xiabo-lab/lyrics/screenshot/carlyric-20260717-191904.png

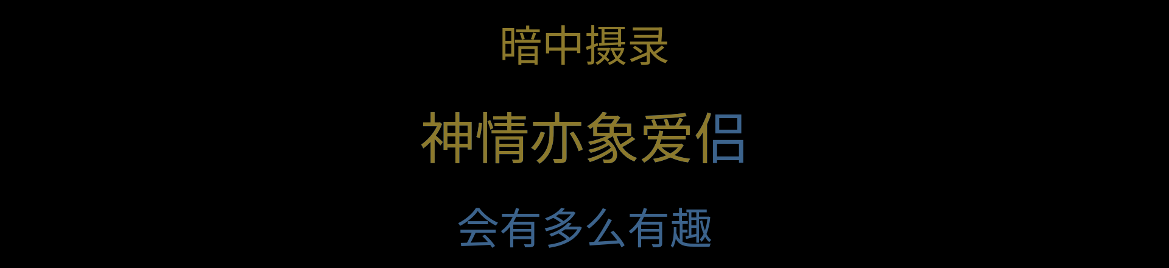
screenshot/carlyric-20260717-191904.png
