xiabo-lab/lyrics/screenshot/carlyric-20260717-194033.png

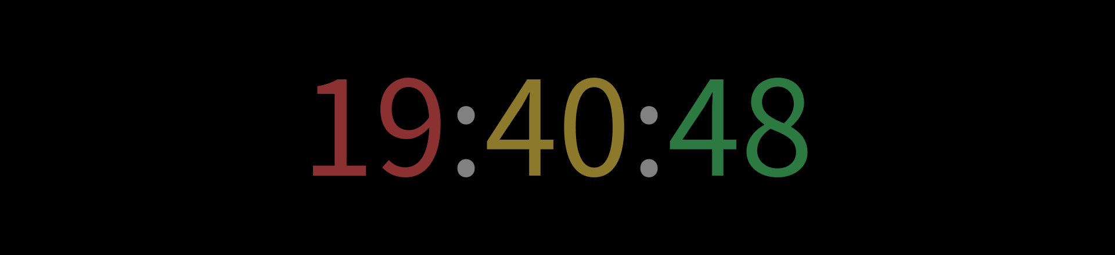
screenshot/carlyric-20260717-194033.png
