xiabo-lab/lyrics/screenshot/carlyric-20260717-194539.png

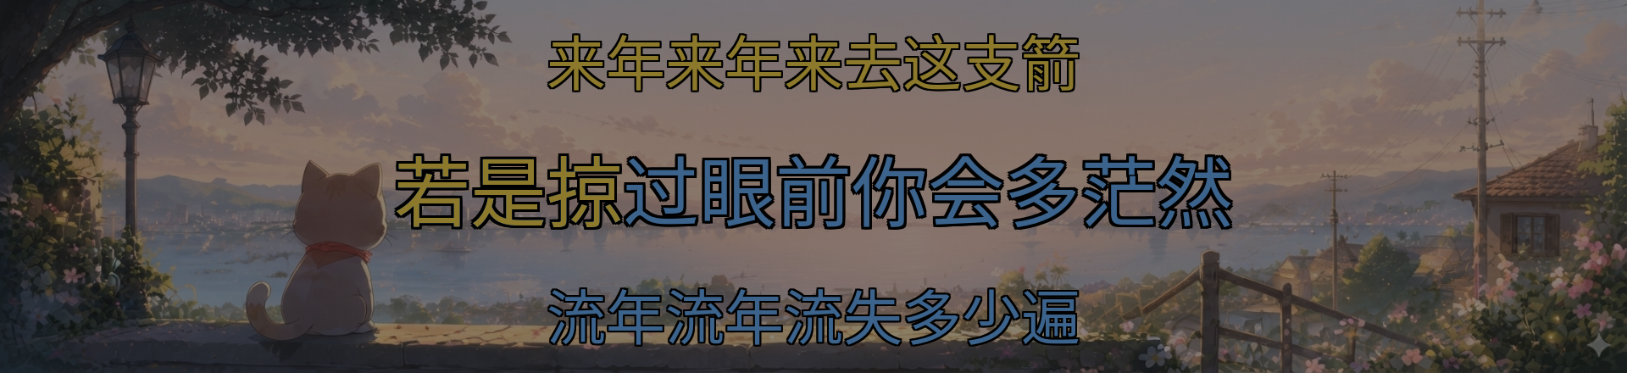
screenshot/carlyric-20260717-194539.png
