xiabo-lab/lyrics/screenshot/carlyric-20260717-200437.png

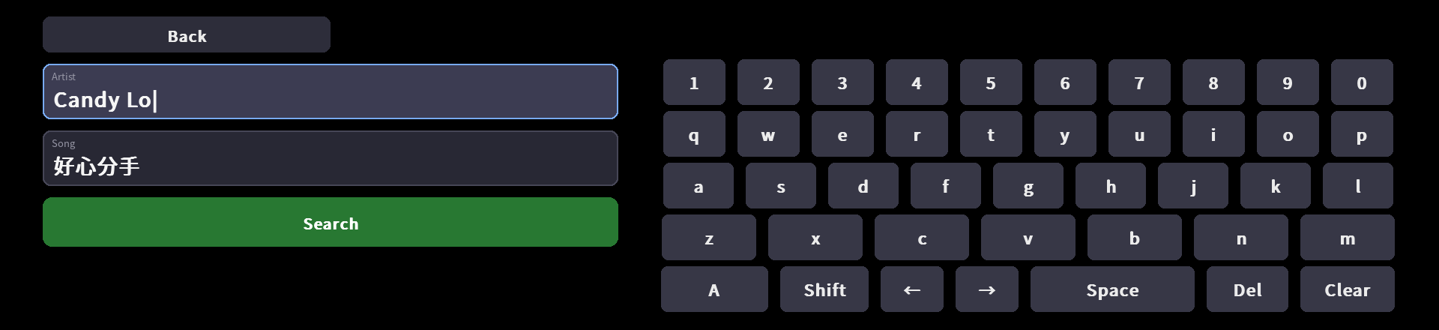
screenshot/carlyric-20260717-200437.png
