xiabo-lab/lyrics/screenshot/live-20260717-205317.png

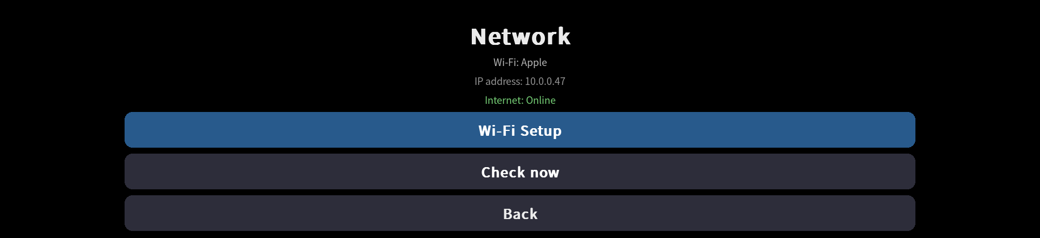
screenshot/live-20260717-205317.png
