xiabo-lab/lyrics/screenshot/menu/01-main-menu.png

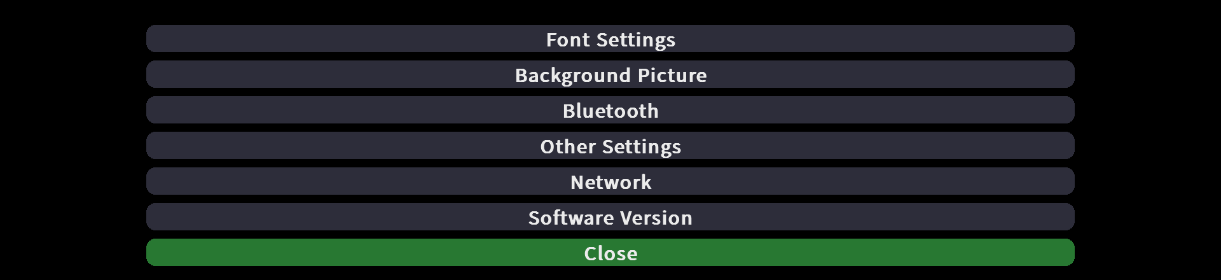
screenshot/menu/01-main-menu.png
