xiabo-lab/lyrics/screenshot/menu/02-font-settings.png

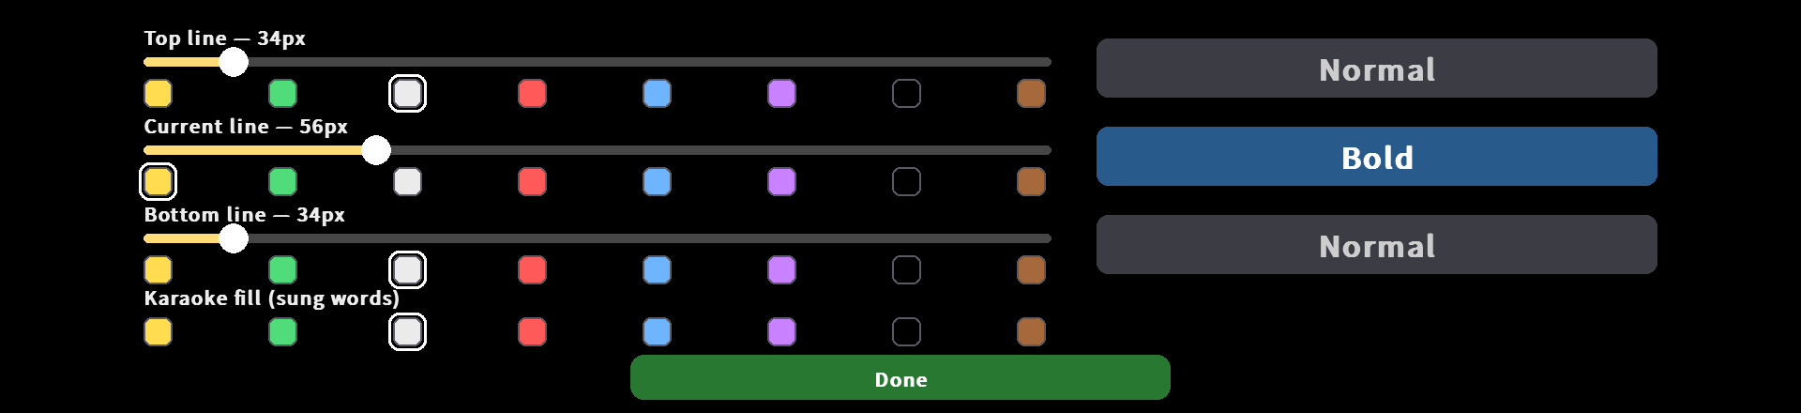
screenshot/menu/02-font-settings.png
