xiabo-lab/lyrics/screenshot/menu/03-background-picture.png

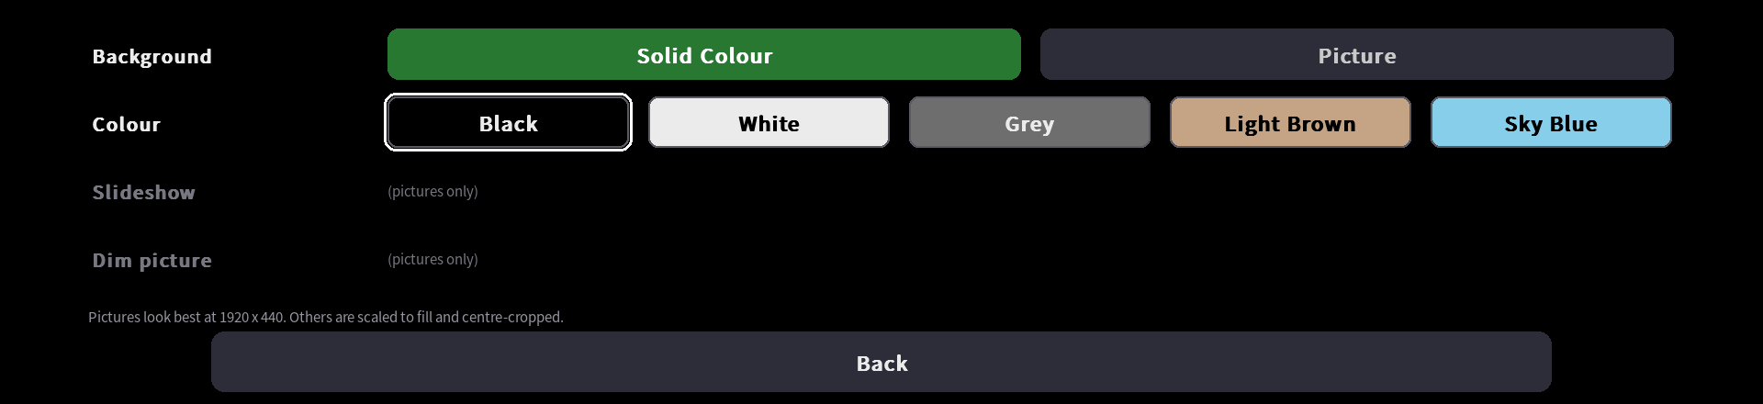
screenshot/menu/03-background-picture.png
