xiabo-lab/lyrics/screenshot/menu/04-bluetooth.png

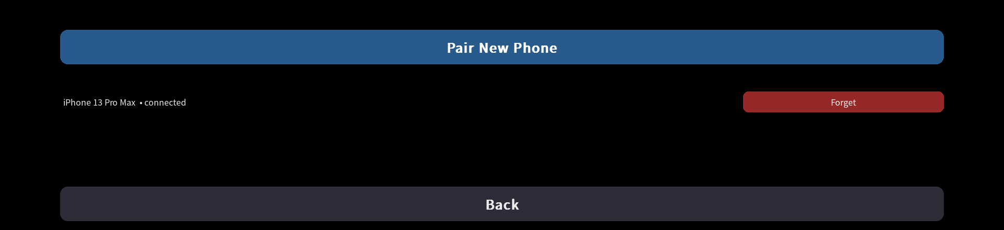
screenshot/menu/04-bluetooth.png
