xiabo-lab/lyrics/screenshot/menu/05-other-settings.png

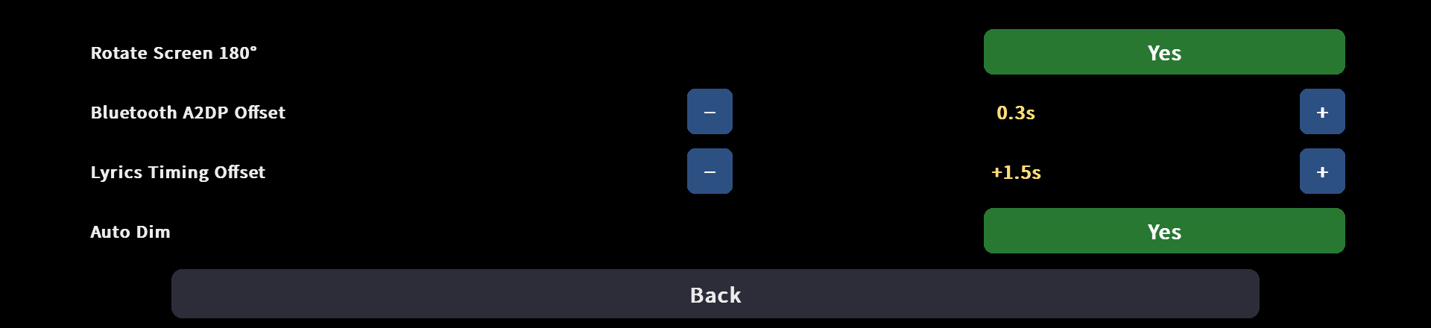
screenshot/menu/05-other-settings.png
