xiabo-lab/lyrics/screenshot/menu/06-network.png

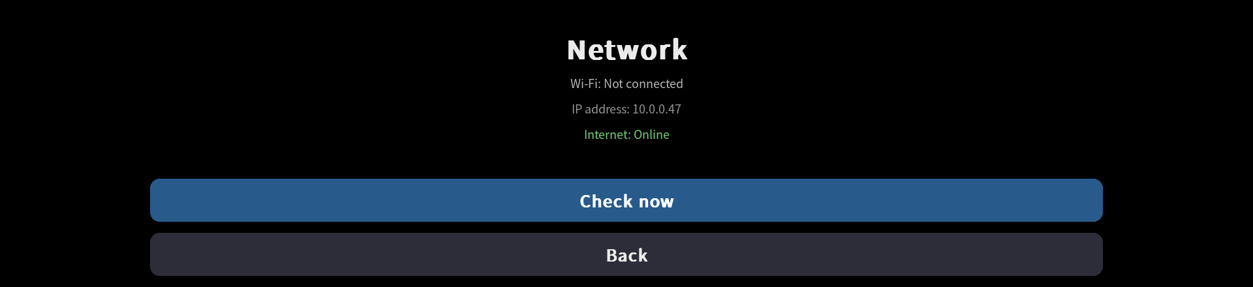
screenshot/menu/06-network.png
