xiabo-lab/lyrics/screenshot/post-ota-20260717-201657.png

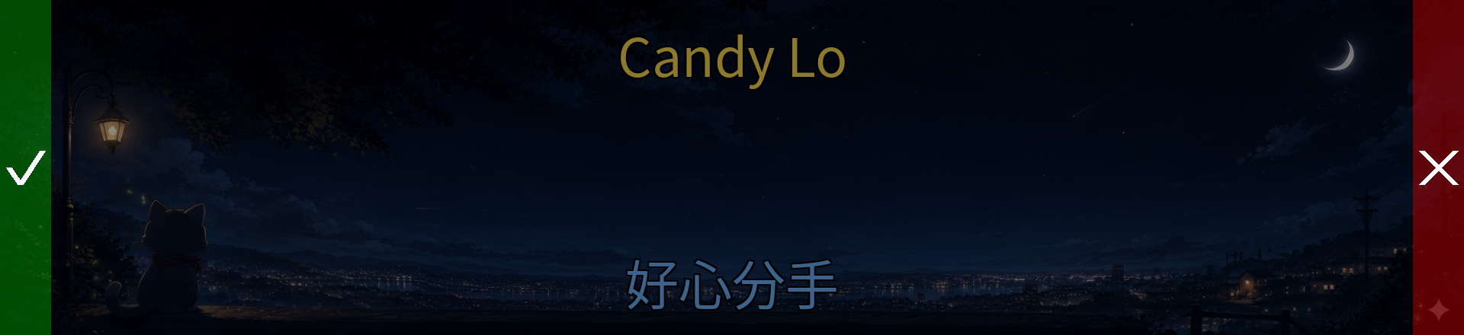
screenshot/post-ota-20260717-201657.png
