xiabo-lab/lyrics/screenshot/wifi/1-list.png

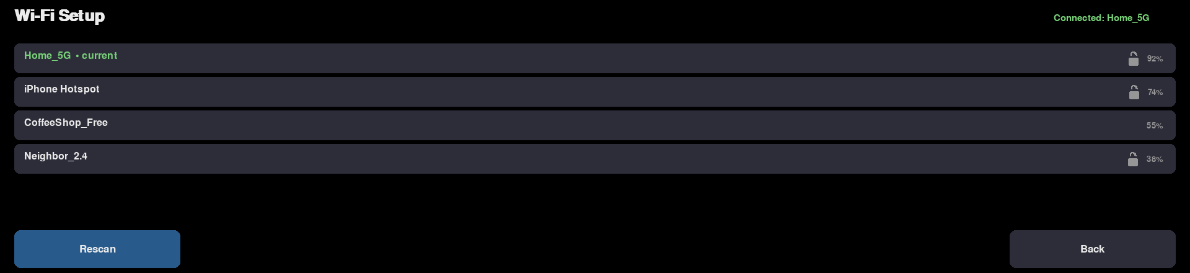
screenshot/wifi/1-list.png
