xiabo-lab/lyrics/screenshot/wifi/2-password.png

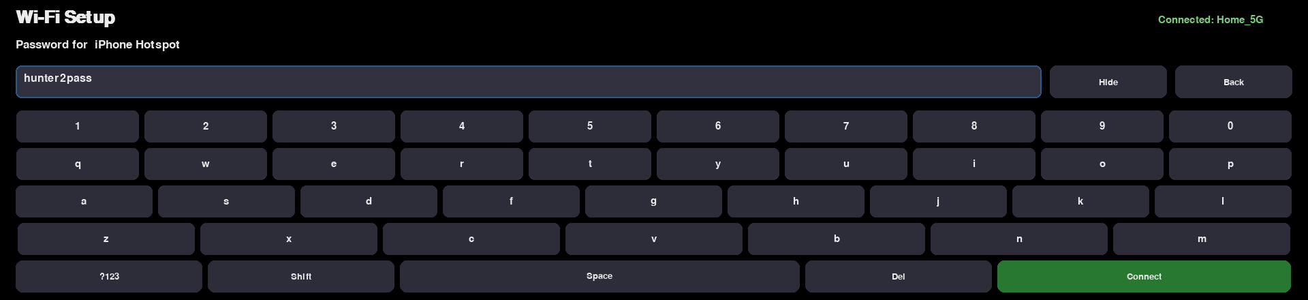
screenshot/wifi/2-password.png
