xiabo-lab/lyrics/screenshot/wifi/3-password-sym.png

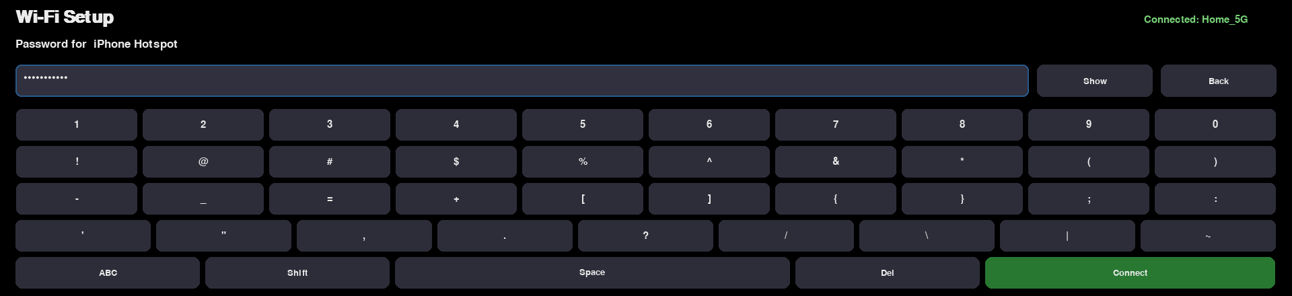
screenshot/wifi/3-password-sym.png
