xiabo-lab/lyrics/Wallpaper/Sample 4.png

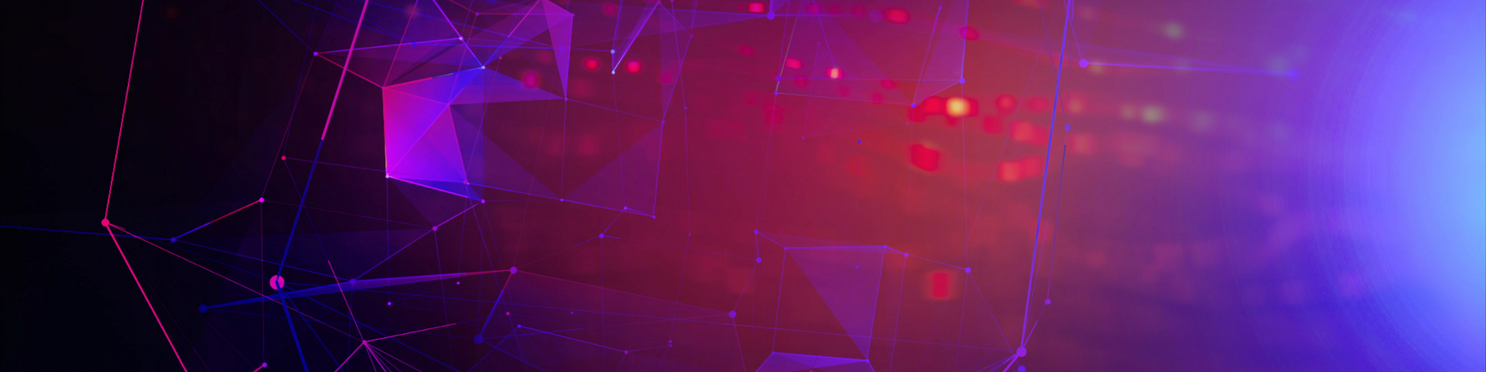
Wallpaper/Sample 4.png
