xiabo-lab/lyrics/Wallpaper/Sample 5.png

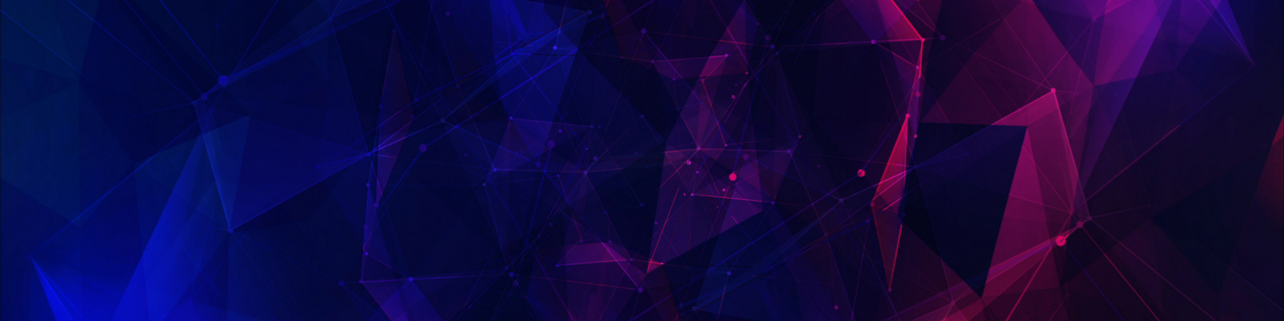
Wallpaper/Sample 5.png
