xiabo-lab/lyrics/Wallpaper/Sample 6.jpg

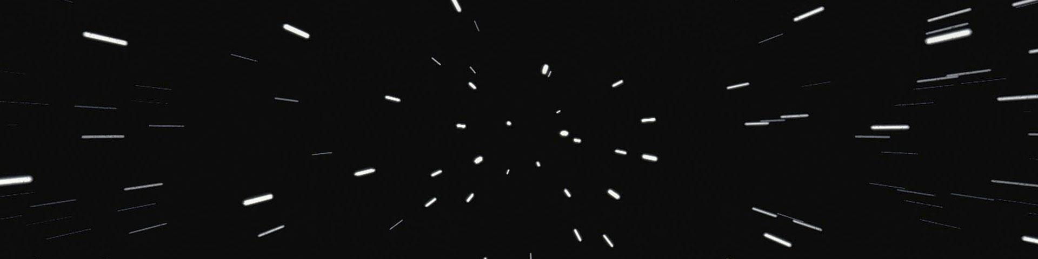
Wallpaper/Sample 6.jpg
