xiabo-lab/lyrics/Wallpaper/Sample 7.jpg

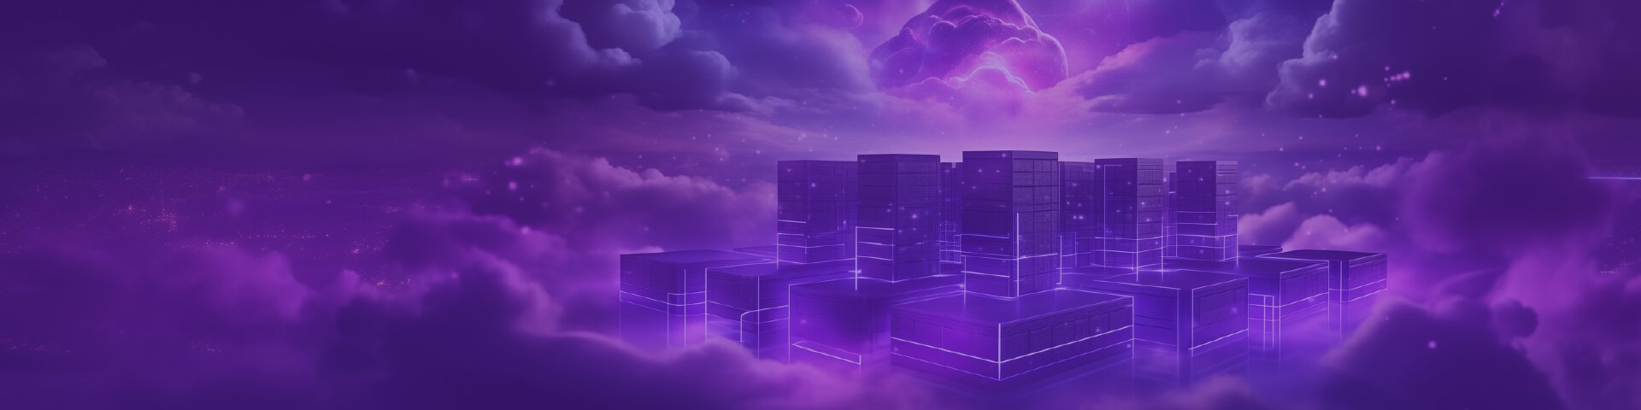
Wallpaper/Sample 7.jpg
