xiabo-lab/lyrics/Wallpaper/Sample 8.jpg

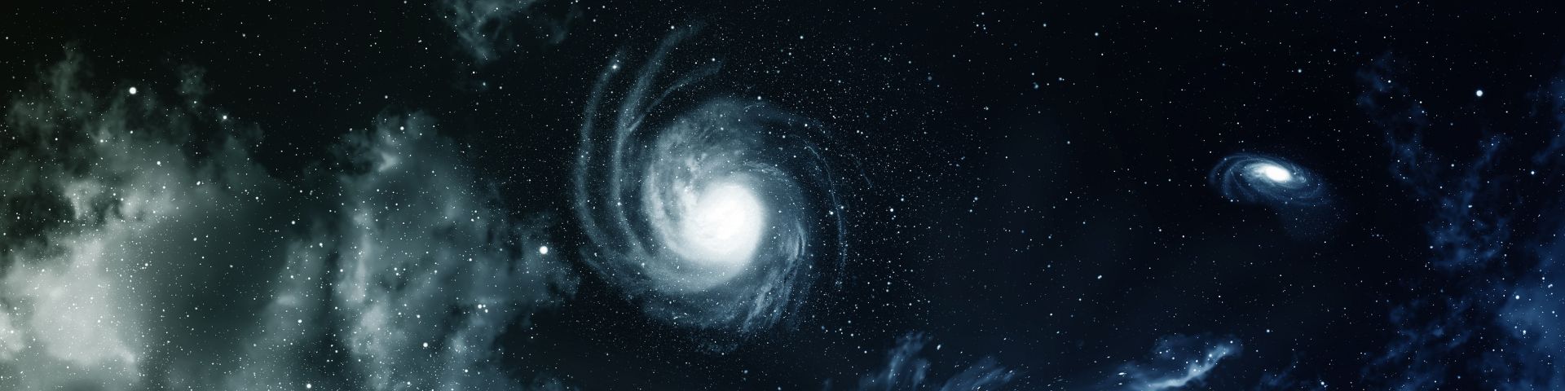
Wallpaper/Sample 8.jpg
