xiabo-lab/lyrics/Wallpaper/Sample 11.png

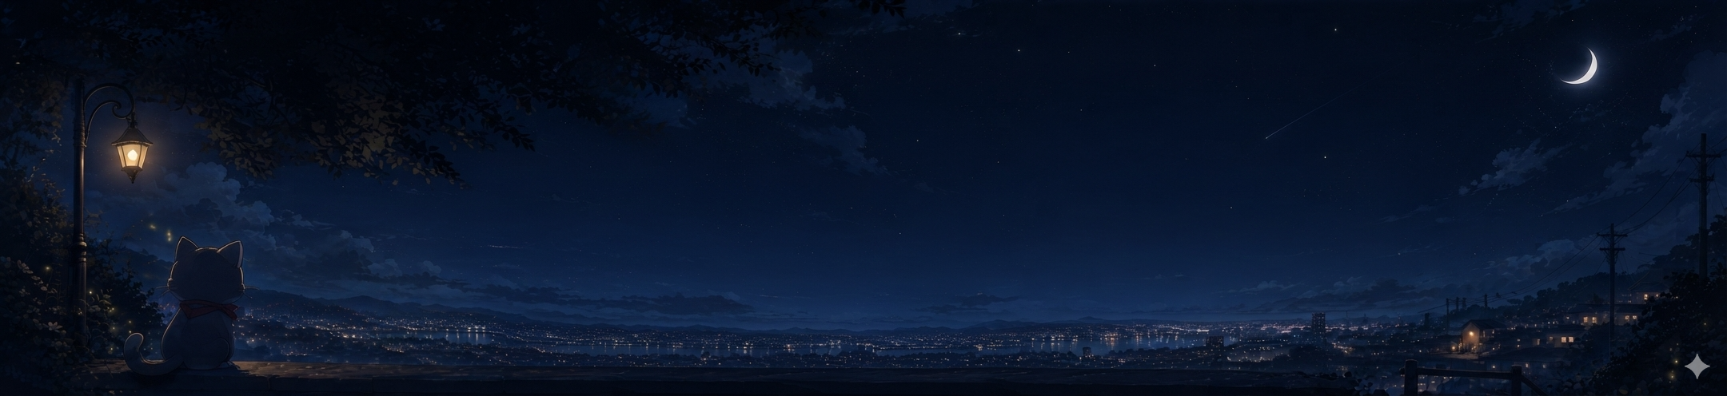
Wallpaper/Sample 11.png
