xiabo-lab/lyrics/Wallpaper/Sample 13.png

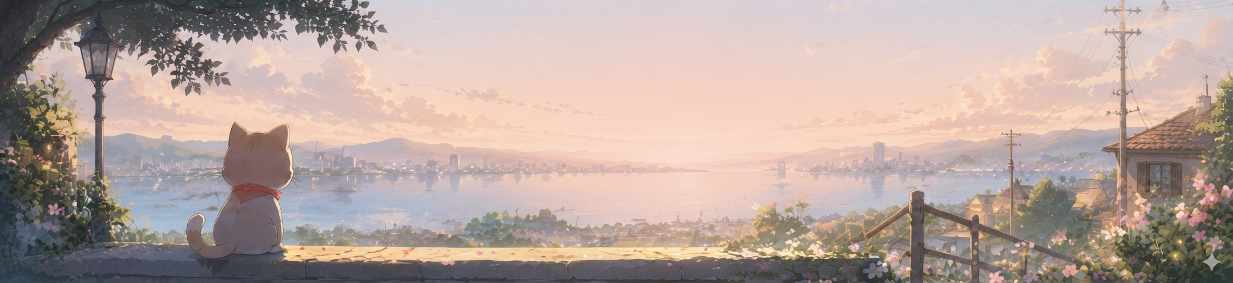
Wallpaper/Sample 13.png
