xiabo-lab/lyrics/screenshot/search-result-20260717-200348.png

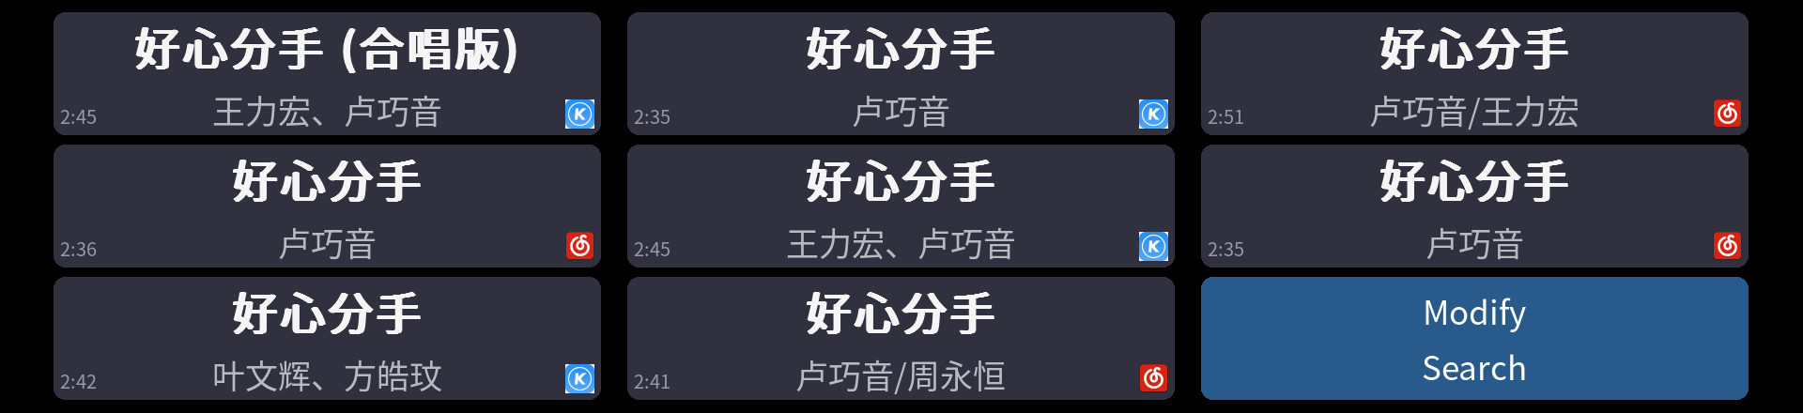
screenshot/search-result-20260717-200348.png
