xiabo-lab/lyrics/screenshot/wifi/4-result-ok.png

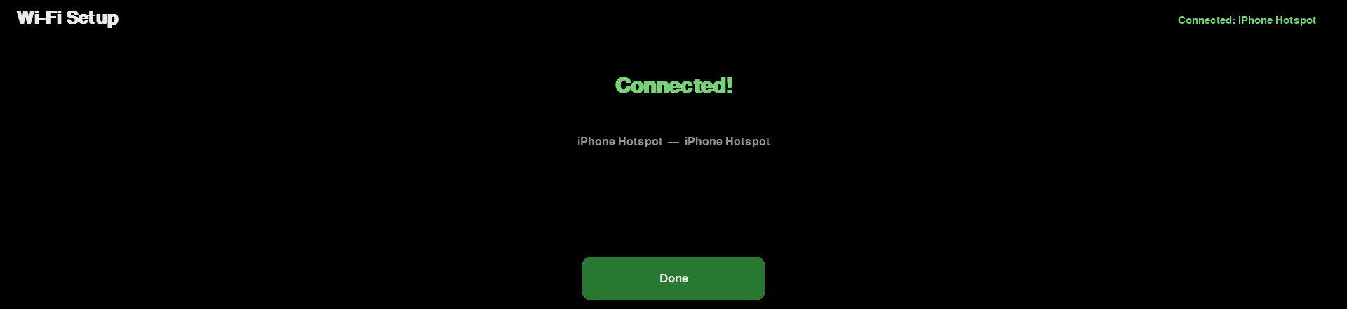
screenshot/wifi/4-result-ok.png
