xiabo-lab/lyrics/screenshot/wifi/7-result-fail-changepw.png

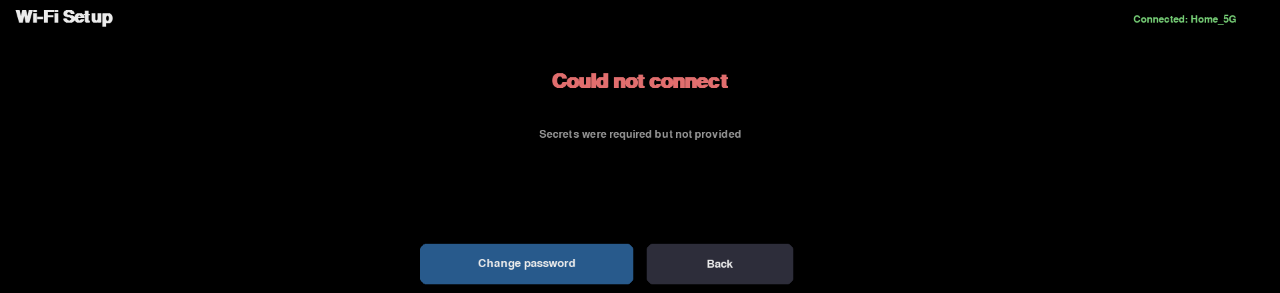
screenshot/wifi/7-result-fail-changepw.png
